samp38/koboy/firmware/filters.h

/* 
 * File:   filters.h
 * Author: sam
 *
 * Created on 9 janvier 2013, 09:04
 */

#ifndef FILTERS_H
#define	FILTERS_H

s32 filterPressure(s32);
s32 speedIIRFilter(s32);
s16 speed_average(s16);


#endif	/* FILTERS_H */
