samp38/koboy/firmware/uart.h

/* 
 * File:   uart.h
 * Author: sam
 *
 * Created on 18 juin 2012, 15:42
 */

#ifndef UART_H
#define	UART_H

void uart2_Config(void);
void uart1_Config(void);

void uart_Print(char *szBuf);


#endif	/* UART_H */
